lanmarc77/esp-audio-book-player/pictures/first_poc.jpg

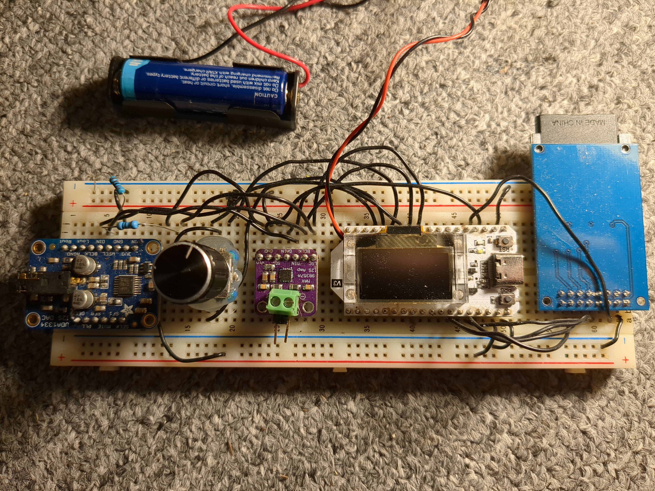
pictures/first_poc.jpg
