lanmarc77/esp-audio-book-player/pictures/mobile_version.jpg

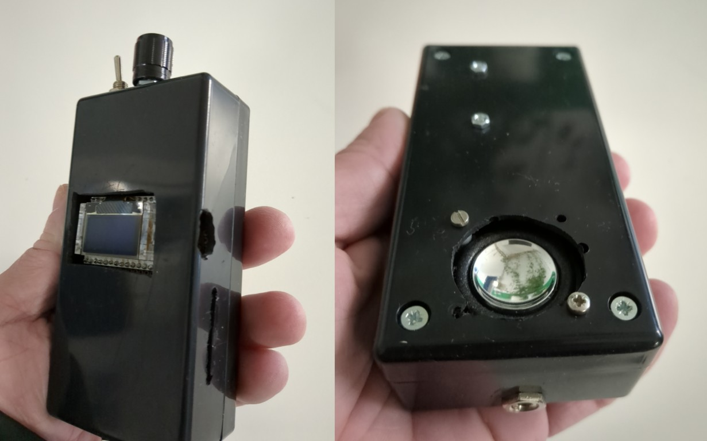
pictures/mobile_version.jpg
