lanmarc77/esp-audio-book-player/src/main/ff_handling.c

/*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
    You should have received a copy of the GNU General Public License
    along with this program.  If not, see <http://www.gnu.org/licenses/>.
*/
#ifndef FF_HANDLING_C
#define FF_HANDLING_C
#include <string.h>
#include "esp_log.h"
#include "esp_vfs.h"
#include "ff_handling.h"
#include "format_helper.h"
#include "sd_card.h"
#include "ui_main.h"

#define FF_LOG_TAG "FF"

/**
  * @brief  gets a sorted list of files or folders inside a given path
  *
  * @param[in] folderPath pointer to full vfs mounted path
  * @param[out] amountOfEntries pointer which holds the number of sorted entries
  * @param[out] sortedArry pointer to an an array which contains the IDs of the found files sorted ascending
  * @param[in] ffType which type of entries to look for: 0=directory, 1=files
  * @param[in] outQueue pointer to a queue handle where the current status of the finding/sorting can be reported for the UI
  * @param[in] inQueue pointer to queue handle to stop the sorting process from the UI, send -1 to request a stop
  * @param[in] searchString pointer to a string of one specific entrystring (usually a filename) whichs sorting position is to be reported in searchId
  * @param[out] searchId pointer to a value which will hold the sorting postion in the sortedIdArray of the file to be searched via searchString
  * 
  * @return 1=ok, finished (-1 is sent to outQueue), 2=folderPath not found (-2 is sent to outQueue)
  *         3=to many entries (-3 is sent to outQueue), 4=canceld sorting/finding as requested (-4 is sent to outQueue)
  */
uint8_t FF_getList(char* folderPath,uint16_t* amountOfEntries,uint16_t* sortedIdArray,uint8_t ffType,QueueHandle_t* outQueue, QueueHandle_t* inQueue, char* searchString,int32_t* searchId){
    uint16_t maxIdCounter=FF_MAX_SORT_ELEMENTS;//limits the files to sort even if more files exist
    struct dirent *currentEntry;
    DIR *dir = NULL;
    char minLastName[FF_FILE_PATH_MAX];
    char minNewCandidateName[FF_FILE_PATH_MAX];
    char fileLine[FF_FILE_PATH_MAX];
    uint16_t sortedPosition=0;
    uint16_t maxFiles=0;
    //uint64_t startTime=esp_timer_get_time();
    *amountOfEntries=0;
    int32_t outQueueMsg=0;
    int32_t inQueueMsg=0;

    //checking for presorted folder list
    if(ffType==0){
        strcpy(&minLastName[0],folderPath);strcat(&minLastName[0],"/presorted.txt");
        FILE* preSortedFile=NULL;
        preSortedFile=fopen(&minLastName[0],"r");
        struct stat st;
        if(preSortedFile!=NULL){
            stat(&minLastName[0], &st);
            while(fgets(&fileLine[0],sizeof(fileLine),preSortedFile)!=NULL){
                uint16_t l=strlen(&fileLine[0]);
                fpos_t currentFilePos=0;
                if(fgetpos(preSortedFile,&currentFilePos)==0){
                    outQueueMsg=(1000*currentFilePos)/st.st_size;
                    xQueueOverwrite(*outQueue,&outQueueMsg);
                }
                if((l>0)&&(fileLine[l-1]==0x0A)){fileLine[l-1]=0; l--;}
                if((l>0)&&(fileLine[l-1]==0x0D)){fileLine[l-1]=0; l--;}
                if((l>0)&&(fileLine[0]!='#')){
                    sortedPosition++;
                    sortedIdArray[sortedPosition-1]=sortedPosition;
                    //ESP_LOGI(FF_LOG_TAG,"Storing %s at %d as %d",&fileLine[0],sortedPosition-1,sortedPosition);
                    *amountOfEntries=sortedPosition;
                    if((searchString!=NULL)&&(searchString[0]!=0)){
                        if(strcasecmp(&fileLine[0],&searchString[0])==0){
                            *searchId=sortedPosition-1;
                            //ESP_LOGI(FF_LOG_TAG,"Found: %s at %d",&fileLine[0],sortedPosition);
                        }
                    }
                }
                if(sortedPosition>=FF_MAX_FOLDER_ELEMENTS){
                    break;
                }
            }
            fclose(preSortedFile);
            outQueueMsg=-1;
            xQueueOverwrite(*outQueue,&outQueueMsg);
            return 1;
        }
    }

    minNewCandidateName[0]=0;
    minLastName[0]=0;
    dir = opendir(folderPath);
    ESP_LOGI(FF_LOG_TAG,"Scanning: %s",folderPath);
    if(dir){
        do{
            uint16_t minNewCandidateID=0,positionCounter=0;
            minNewCandidateName[0]=0;
            while (((currentEntry = readdir(dir)) != NULL)&&(positionCounter<maxIdCounter)) {
                if(currentEntry->d_name[0]=='?') continue; //name contains invalid charactes for current code page
                if((ffType==0)&&(currentEntry->d_type!=DT_DIR)){//directory needs to be directory type
                    continue;
                }else if((ffType==1)&&(currentEntry->d_type==DT_DIR)){//file is not allowed to have directory type
                    continue;
                }
                if(ffType==0){
                    if(strcmp(&currentEntry->d_name[0],FW_DIR_NAME)==0){//ignore fwupgrade directory
                        continue;
                    }
                }
                if(ffType==1){//check valid file extensions
                    uint8_t fileFormat=FORMAT_HELPER_getFileType(&currentEntry->d_name[0]);
                    if((fileFormat==FORMAT_HELPER_FILE_TYPE_UNKNOWN)||(fileFormat==FORMAT_HELPER_FILE_TYPE_M4A)){
                        //mpeg4 audio is too buggy and picky in esp-adf
                        continue;
                    }
                }
                if(strcmp(currentEntry->d_name,&minLastName[0])>0){//it is only a new candidate if it is greater then the last minimum
                    if(minNewCandidateName[0]==0){
                        strcpy(&minNewCandidateName[0],currentEntry->d_name);
                        minNewCandidateID=positionCounter+1;
                    }
                    if(strcmp(currentEntry->d_name,&minNewCandidateName[0])<0){//the current entry is smaller, make it the new candidate
                        strcpy(&minNewCandidateName[0],currentEntry->d_name);
                        minNewCandidateID=positionCounter+1;
                    }
                }
                positionCounter++;
                if(positionCounter>=maxIdCounter){
                    outQueueMsg=-3;
                    closedir(dir);
                    xQueueOverwrite(*outQueue,&outQueueMsg);
                    return 3;
                }
                
                if(xQueueReceive(*inQueue,&inQueueMsg,0)== pdPASS){
                    if(inQueueMsg==-1){
                        outQueueMsg=-4;
                        closedir(dir);
                        xQueueOverwrite(*outQueue,&outQueueMsg);
                        return 4;
                    }
                }
            }
            maxFiles=positionCounter;
            *amountOfEntries=sortedPosition;
            if(minNewCandidateName[0]!=0){
                rewinddir(dir);
                strcpy(&minLastName[0],&minNewCandidateName[0]);

                double percentDone=(100.0*sortedPosition)/maxFiles;
                outQueueMsg=(int32_t)(percentDone*10);
                xQueueOverwrite(*outQueue,&outQueueMsg);
                //uint64_t timeDiffS=(esp_timer_get_time()-startTime)/1000000;
                //uint64_t timeLeftS=((100*timeDiffS)/percentDone)-timeDiffS;
                //ESP_LOGI(FF_LOG_TAG,"Sort: %s  (%d)  %i/%i  %.1f%%  %llu:%02llu",&minNewCandidateName[0],minNewCandidateID,sortedPosition,maxFiles,percentDone,timeLeftS/60,timeLeftS%60);
                if((searchString!=NULL)&&(searchString[0]!=0)){
                    if(strcasecmp(&minNewCandidateName[0],&searchString[0])==0){
                        *searchId=sortedPosition;
                    }
                }
                sortedIdArray[sortedPosition++]=minNewCandidateID;
                //ESP_LOGI(FF_LOG_TAG,"Storing %s at %d as %d",&minLastName[0],sortedPosition-1,minNewCandidateID);
            }
        }while(minNewCandidateName[0]!=0);
        closedir(dir);
    }else{
        outQueueMsg=-2;
        xQueueOverwrite(*outQueue,&outQueueMsg);
        return 2;
    }
    outQueueMsg=-1;
    xQueueOverwrite(*outQueue,&outQueueMsg);
    return 1;
}

char FF_getNameByIdCacheFolderName[FF_FILE_PATH_MAX];
int32_t FF_getNameByIdCacheId=-1;

/**
  * @brief  gets a file/foldername inside a path by a given ID (position inside FAT)
  *
  * @param[in] folderBasePath pointer to full vfs mounted path
  * @param[in] ID ID of file
  * @param[out] resultName pointer to a char array where the name will be stored
  * @param[in] ffType which type of entries to look for: 0=directory, 1=files
  * 
  * @return 0=ok, file found, 1=folderBasePath not found, 2=file not found
  */
uint8_t FF_getNameByID(char* folderBasePath,uint16_t ID,char *resultName,uint8_t ffType){
    struct dirent *currentEntry;
    /*if(folderBasePath[strlen(folderBasePath)-1]!='/'){
        strcat(folderBasePath,"/");
    }*/
    char fileLine[FF_FILE_PATH_MAX];
    char preSortedFileName[FF_FILE_PATH_MAX];
    DIR *dir = NULL;
    uint16_t idCounter=0;
    
    //ESP_LOGI(FF_LOG_TAG,"Requested: %d",ID);
    //checking for presorted folder list
    if(ffType==0){
        if((FF_getNameByIdCacheId>=0)&&(FF_getNameByIdCacheId==ID)){
            strcpy(resultName,&FF_getNameByIdCacheFolderName[0]);
            return 0;
        }
        UI_MAIN_cpuFull();
        strcpy(&preSortedFileName[0],folderBasePath);strcat(&preSortedFileName[0],"/presorted.txt");
        FILE* preSortedFile=NULL;
        preSortedFile=fopen(&preSortedFileName[0],"r");
        if(preSortedFile!=NULL){
            while(fgets(&fileLine[0],sizeof(fileLine),preSortedFile)!=NULL){
                uint16_t l=strlen(&fileLine[0]);
                if((l>0)&&(fileLine[l-1]==0x0A)){fileLine[l-1]=0; l--;}
                if((l>0)&&(fileLine[l-1]==0x0D)){fileLine[l-1]=0; l--;}
                if((l>0)&&(fileLine[0]!='#')){
                    idCounter++;
                    if(idCounter==ID){
                        //ESP_LOGI(FF_LOG_TAG,"Found2: %d %s",ID,&fileLine[0]);
                        strcpy(resultName,&fileLine[0]);
                        FF_getNameByIdCacheId=ID;
                        strcpy(&FF_getNameByIdCacheFolderName[0],&fileLine[0]);
                        fclose(preSortedFile);
                        UI_MAIN_cpuNormal();
                        return 0;
                    }
                }
            }
            fclose(preSortedFile);
            UI_MAIN_cpuNormal();
            return 2;
        }
    }

    dir = opendir(folderBasePath);
    if(dir){
        while ((currentEntry = readdir(dir)) != NULL) {
            if((ffType==0)&&(currentEntry->d_type!=DT_DIR)){//directory needs to be directory type
                continue;
            }else if((ffType==1)&&(currentEntry->d_type==DT_DIR)){//file is not allowed to have directory type
                continue;
            }
            if(ffType==1){//check valid file extensions
                uint8_t fileFormat=FORMAT_HELPER_getFileType(&currentEntry->d_name[0]);
                if((fileFormat==FORMAT_HELPER_FILE_TYPE_UNKNOWN)||(fileFormat==FORMAT_HELPER_FILE_TYPE_M4A)){
                    //mpeg4 audio is too buggy and picky in esp-adf
                    continue;
                }
            }
            if(ffType==0){
                if(strcmp(&currentEntry->d_name[0],FW_DIR_NAME)==0){//ignore fwupgrade directory
                    continue;
                }
            }
            if(idCounter+1==ID){
                strcpy(resultName,currentEntry->d_name);
                closedir(dir);
                return 0;
            }
            idCounter++;
        }
        closedir(dir);
    }else{
        return 1;
    }
    return 2;
}

#endif
